The-Art-of-Making/AoM-IoT-Bit/Diagrams/code-flowchart-v2.0.png

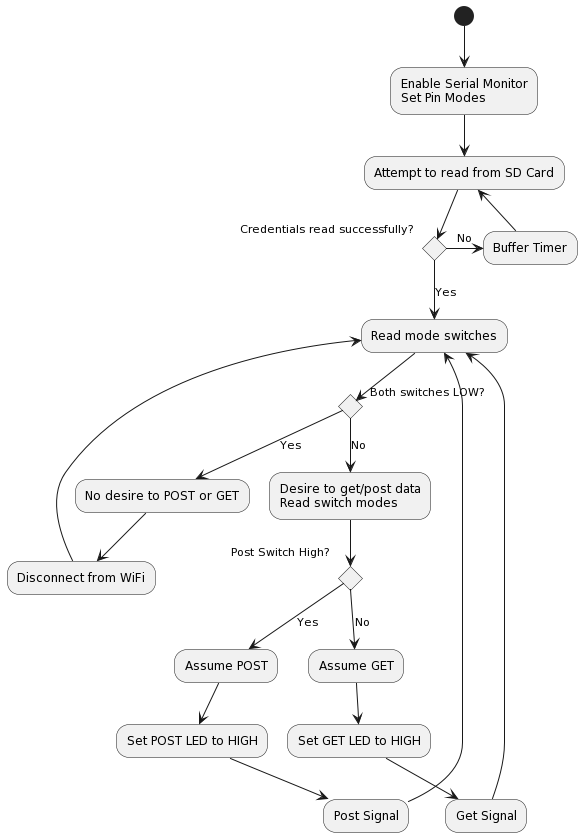
Diagrams/code-flowchart-v2.0.png
