The-Art-of-Making/AoM-IoT-Bit/Diagrams/get-hello-world.jpg

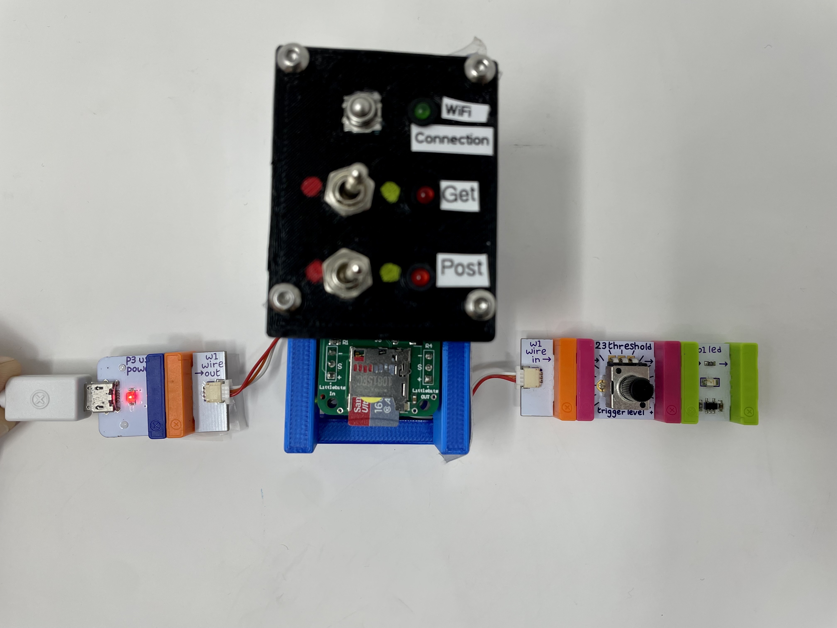
Diagrams/get-hello-world.jpg
