The-Art-of-Making/AoM-IoT-Bit/Diagrams/logic-level-converter.png

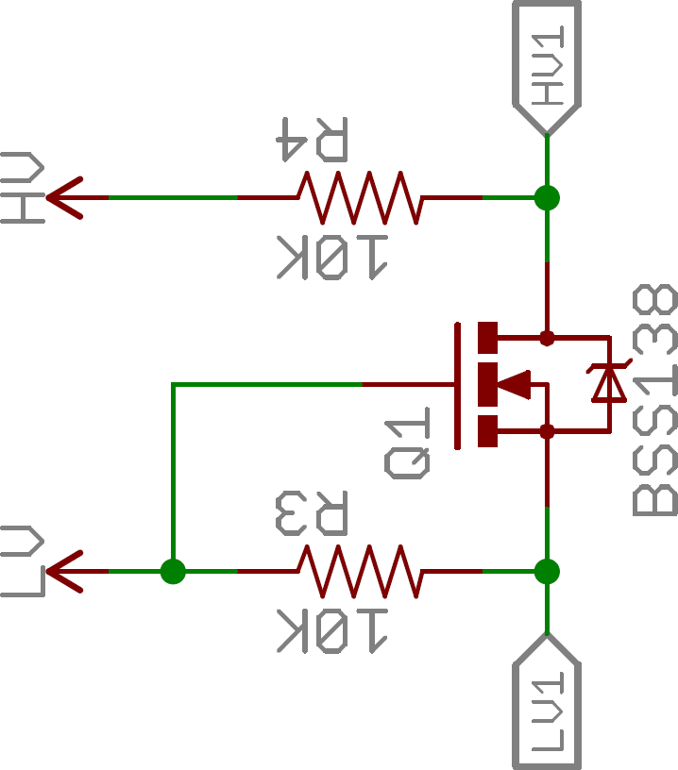
Diagrams/logic-level-converter.png
