The-Art-of-Making/AoM-IoT-Bit/Diagrams/post-hello-world.jpg

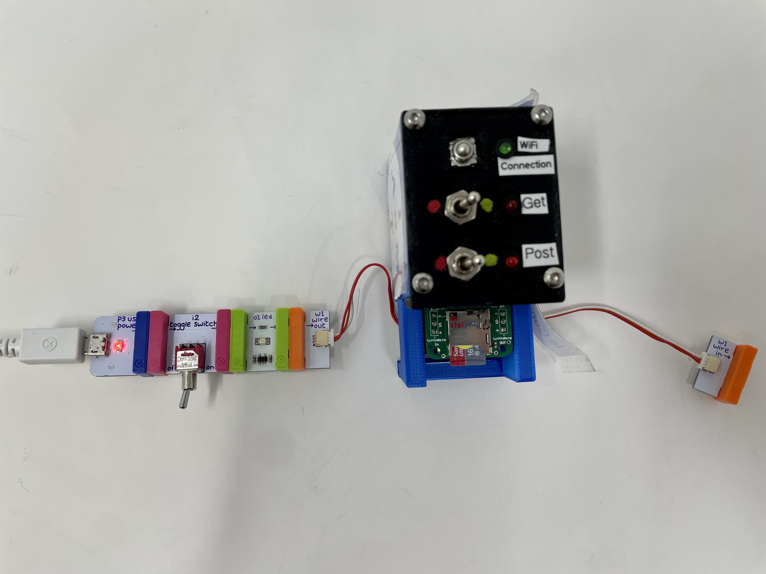
Diagrams/post-hello-world.jpg
