The-Art-of-Making/AoM-IoT-Bit/Diagrams/system-Diagram-No-IFTTT.png

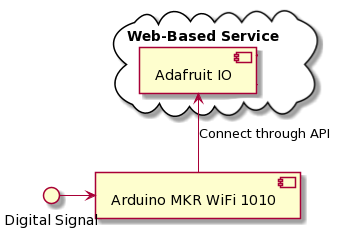
Diagrams/system-Diagram-No-IFTTT.png
