The-Art-of-Making/AoM-IoT-Bit/Diagrams/system-Diagram.png

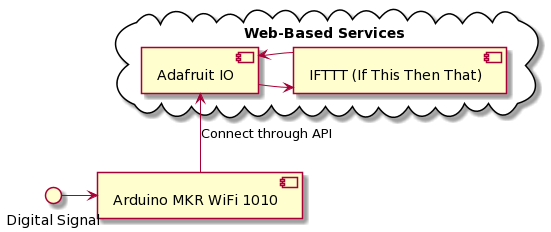
Diagrams/system-Diagram.png
