The-Art-of-Making/AoM-IoT-Bit/media/REV_3/AoM-IoT-bit-Housing-render-v64.png

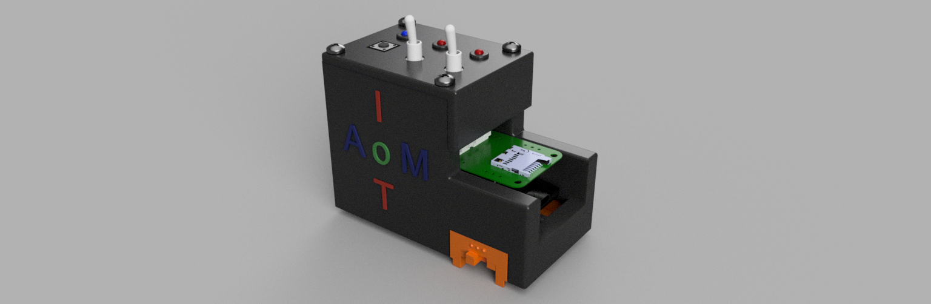
media/REV_3/AoM-IoT-bit-Housing-render-v64.png
