The-Art-of-Making/AoM-IoT-Bit/media/REV_3/cable-diagram_LEDs.png

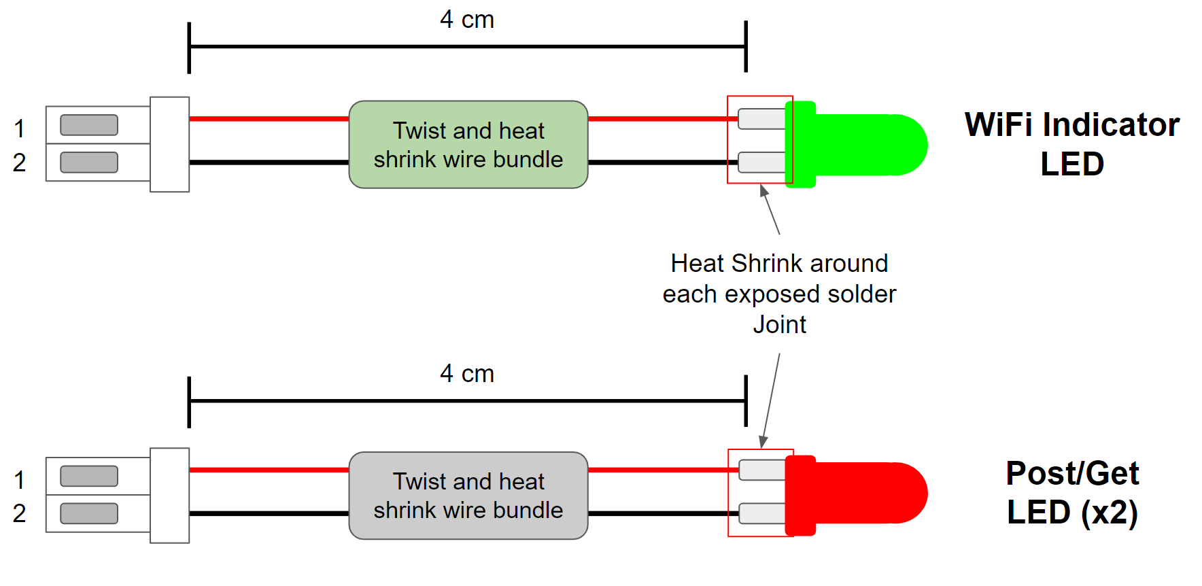
media/REV_3/cable-diagram_LEDs.png
