The-Art-of-Making/AoM-IoT-Bit/media/REV_3/cable-diagram_wire-bits.png

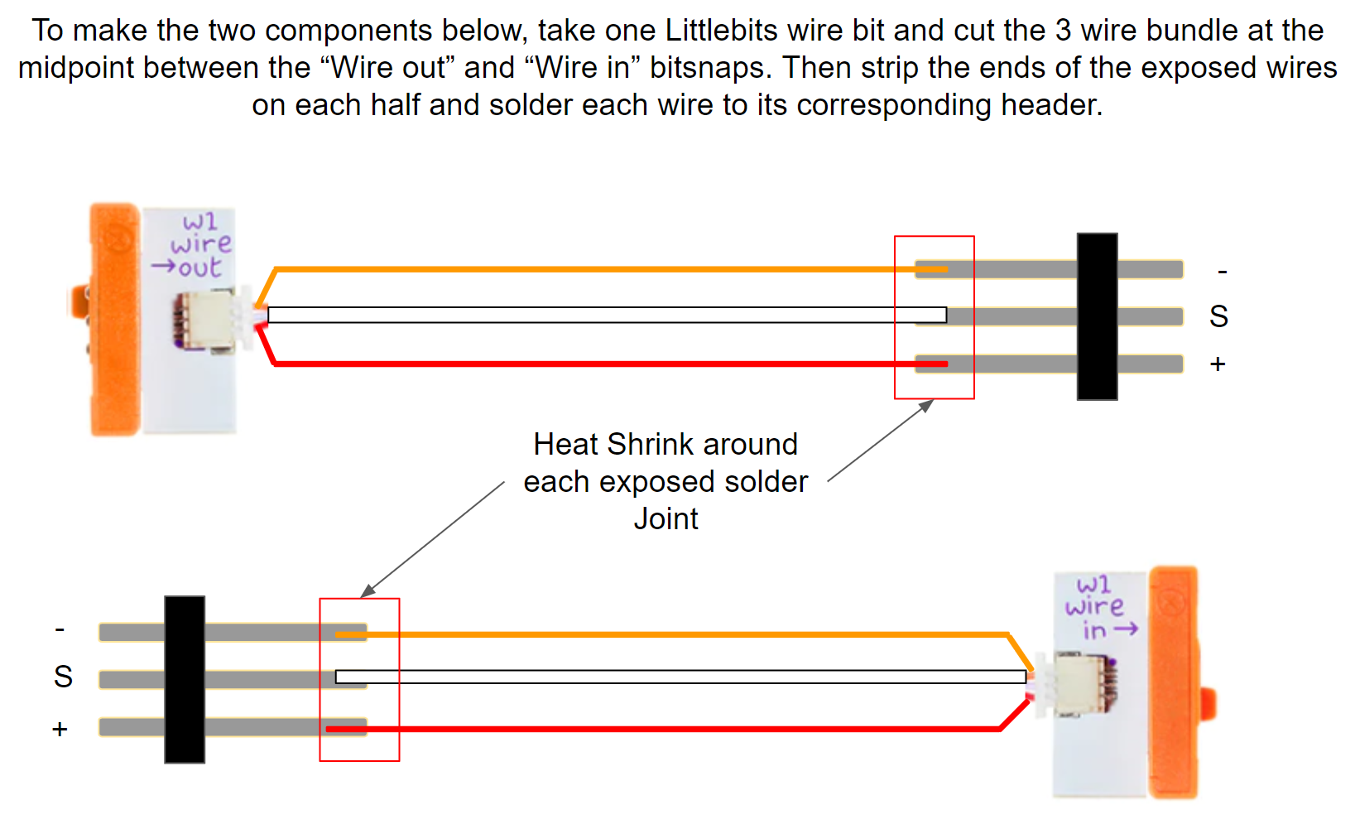
media/REV_3/cable-diagram_wire-bits.png
