The-Art-of-Making/AoM-IoT-Bit/media/REV_3/cloud-feeds.png

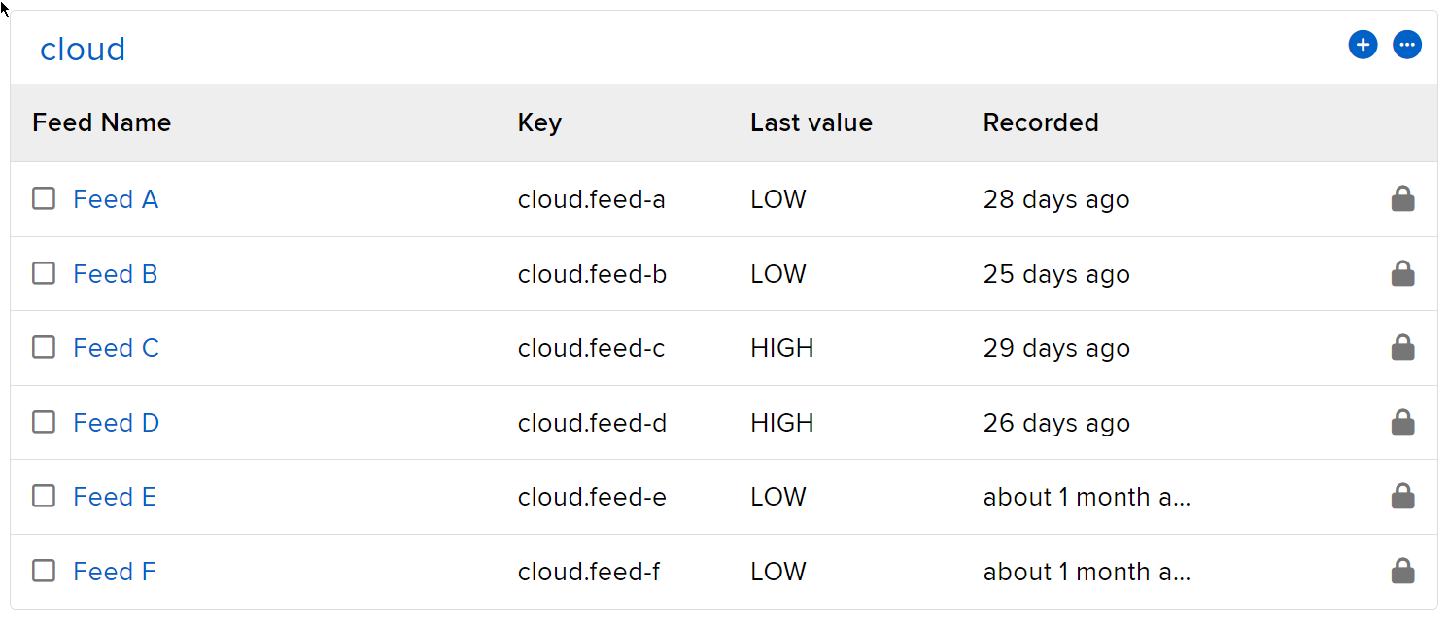
media/REV_3/cloud-feeds.png
