The-Art-of-Making/AoM-IoT-Bit/media/REV_3/GUI-folded.png

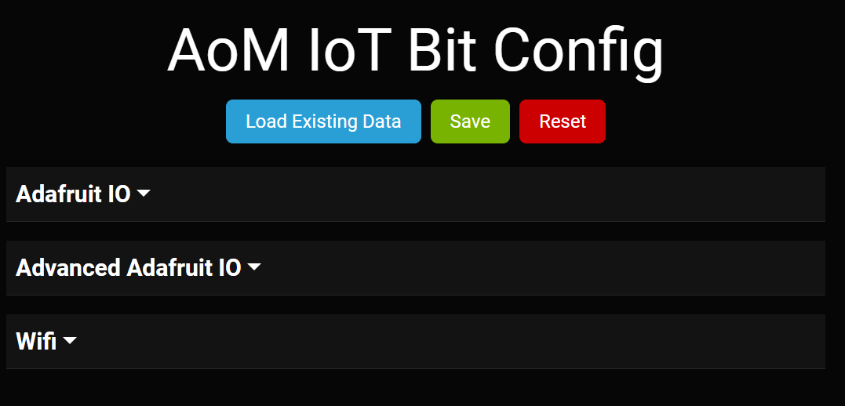
media/REV_3/GUI-folded.png
