The-Art-of-Making/AoM-IoT-Bit/media/REV_3/GUI-IO.png

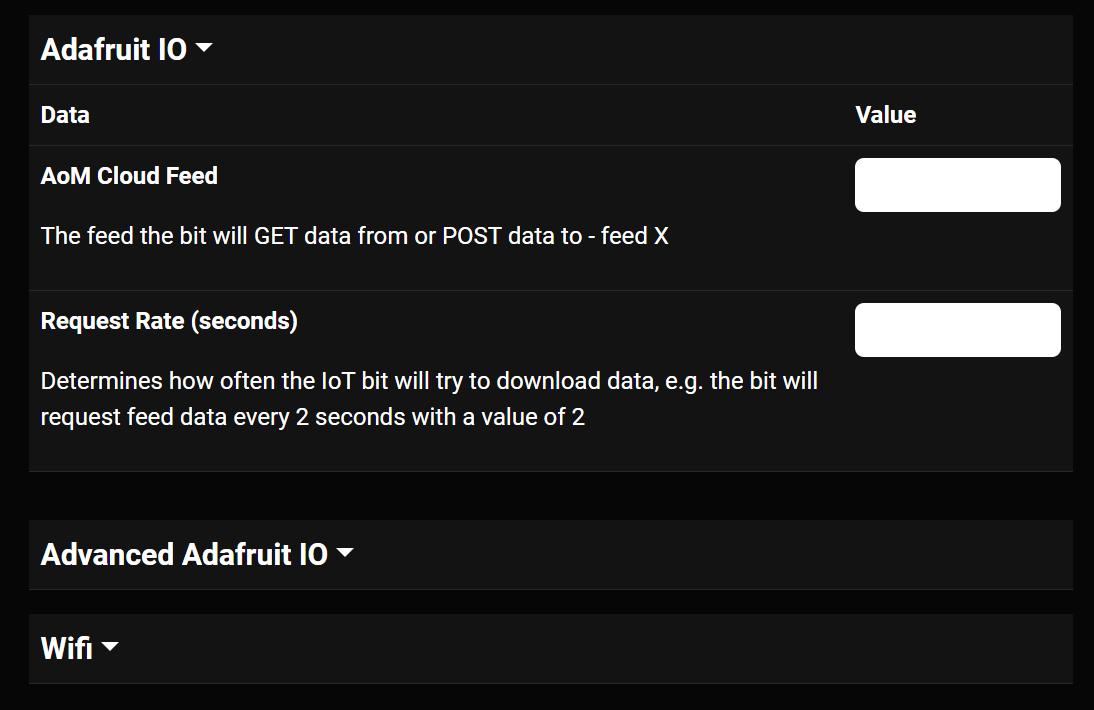
media/REV_3/GUI-IO.png
