The-Art-of-Making/AoM-IoT-Bit/media/REV_3/GUI-WiFi.png

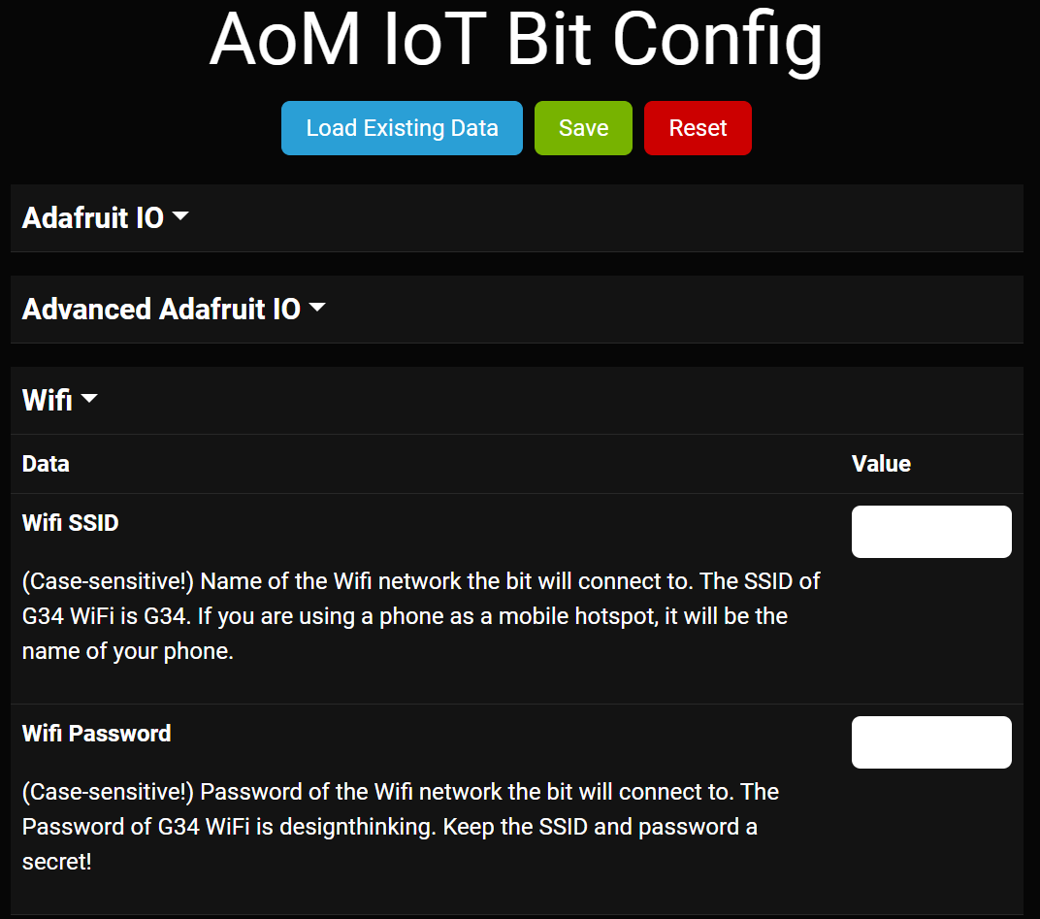
media/REV_3/GUI-WiFi.png
