The-Art-of-Making/AoM-IoT-Bit/media/REV_3/IoT-Bit-v3.0.jpg

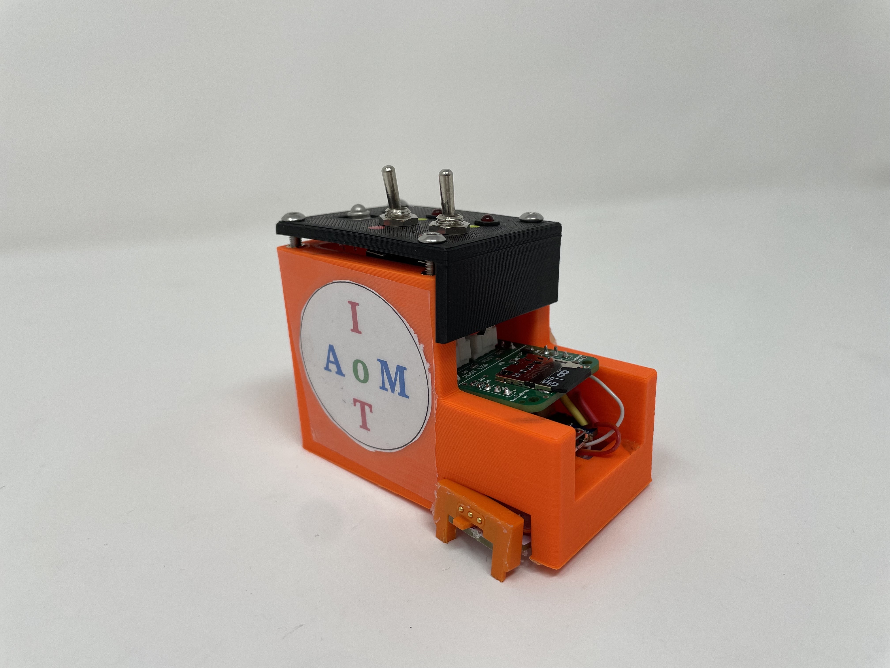
media/REV_3/IoT-Bit-v3.0.jpg
