The-Art-of-Making/AoM-IoT-Bit/media/REV_3/pcb-v1-top.png

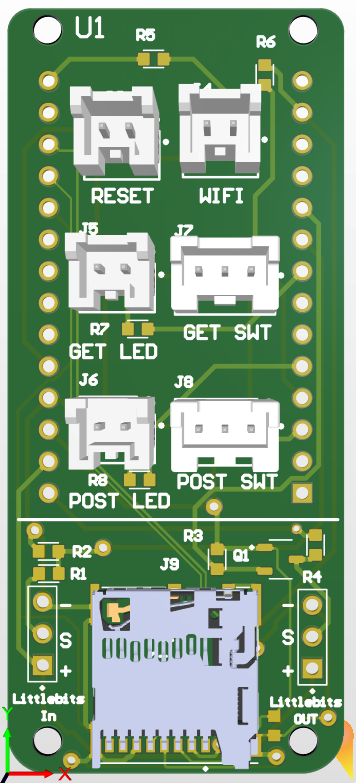
media/REV_3/pcb-v1-top.png
